percentchunk/hydrogenElectrolyzer/Image files/Full stand unrendered.jpeg

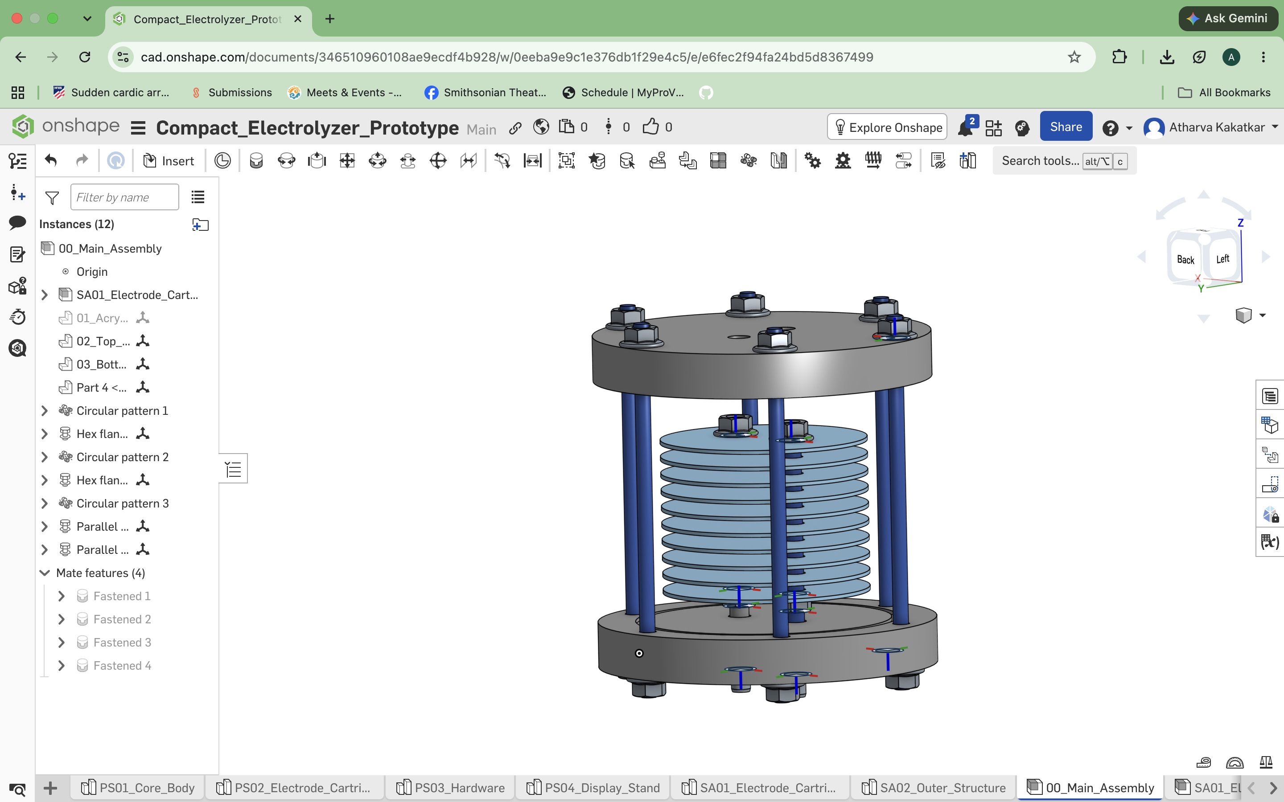
Image files/Full stand unrendered.jpeg
