percentchunk/hydrogenElectrolyzer/Image files/Full stand.jpeg

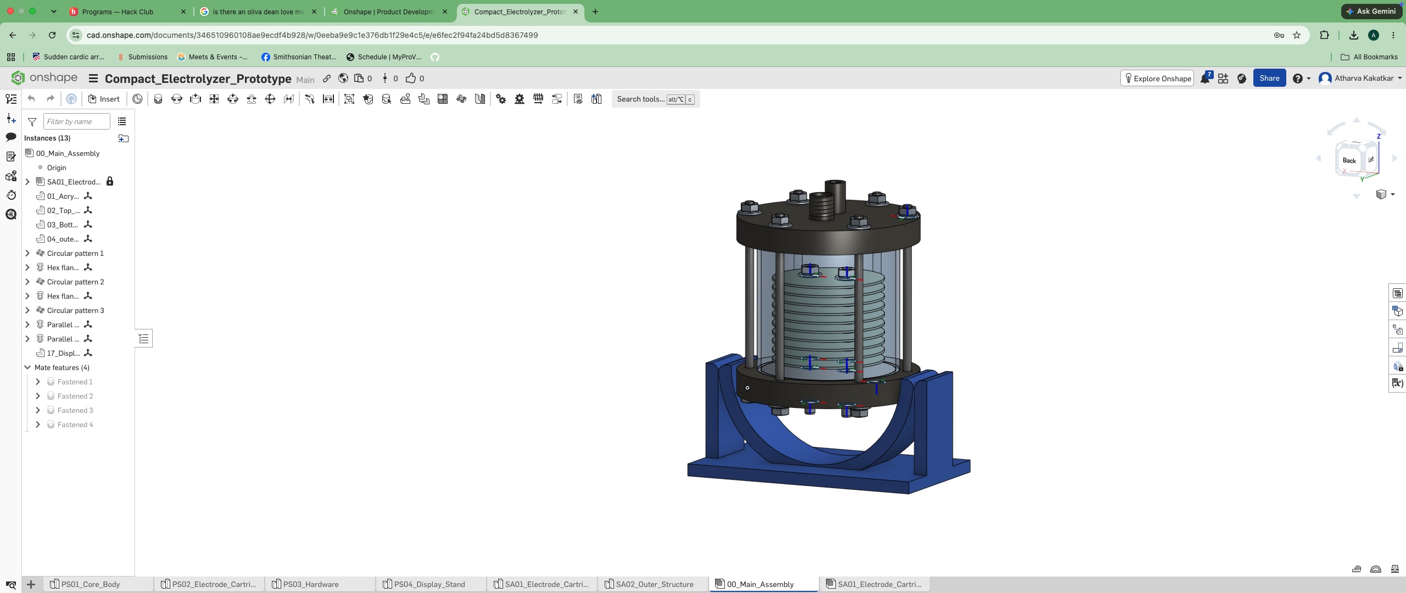
Image files/Full stand.jpeg
